jeffqchen/PS2VGA/Pics/3dprinting.jpg

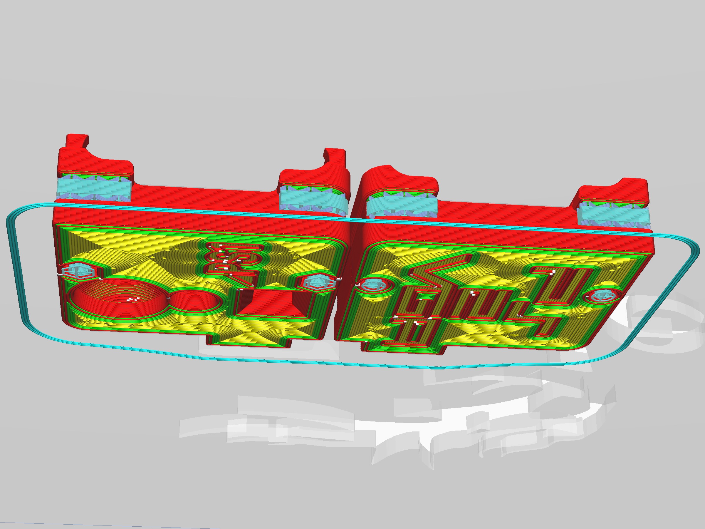
Pics/3dprinting.jpg
