jeffqchen/PS2VGA/Pics/ha_hole.jpg

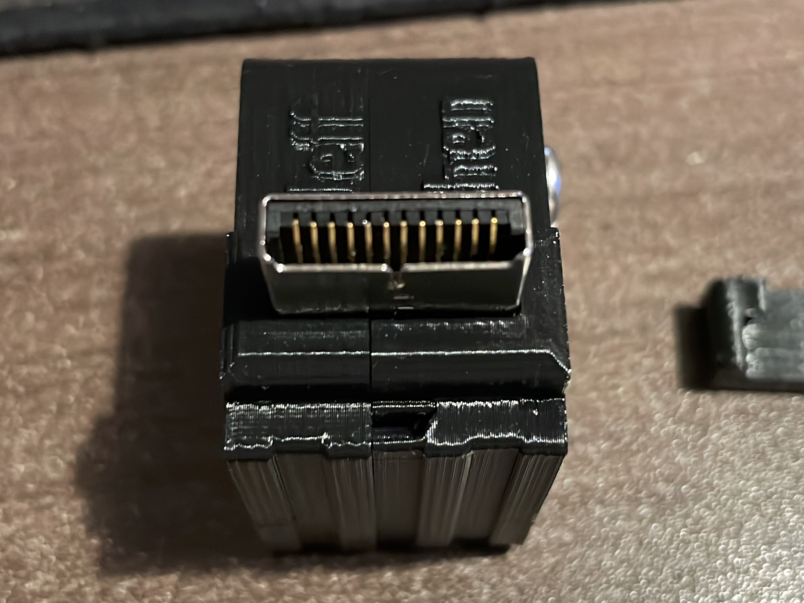
Pics/ha_hole.jpg
