jeffqchen/PS2VGA/Pics/ha_in.jpg

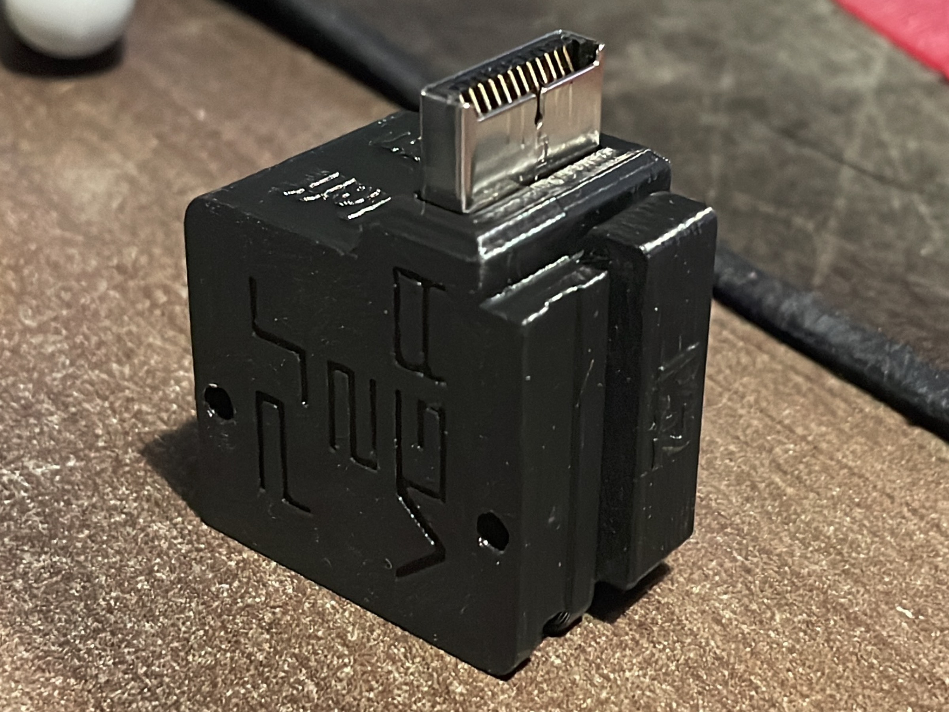
Pics/ha_in.jpg
