jeffqchen/PS2VGA/Pics/ha_ps1.jpg

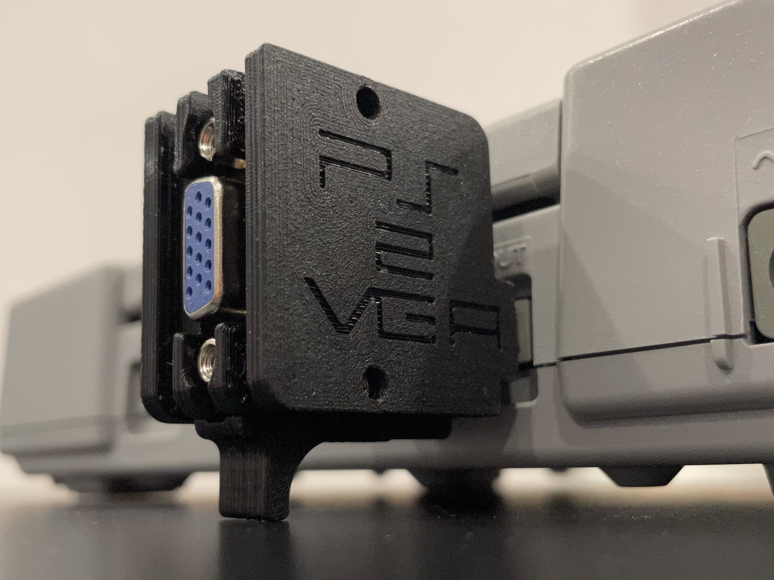
Pics/ha_ps1.jpg
