jeffqchen/PS2VGA/Pics/ha_ps2_l.jpg

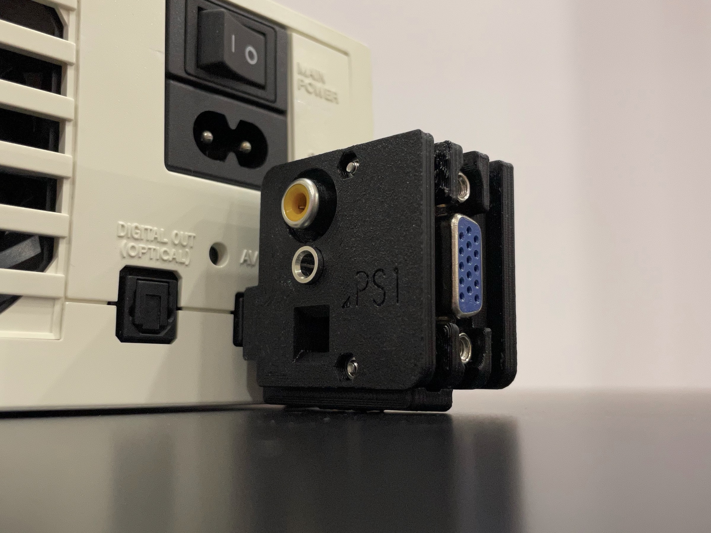
Pics/ha_ps2_l.jpg
