jeffqchen/PS2VGA/Pics/ha_ps2_r.jpg

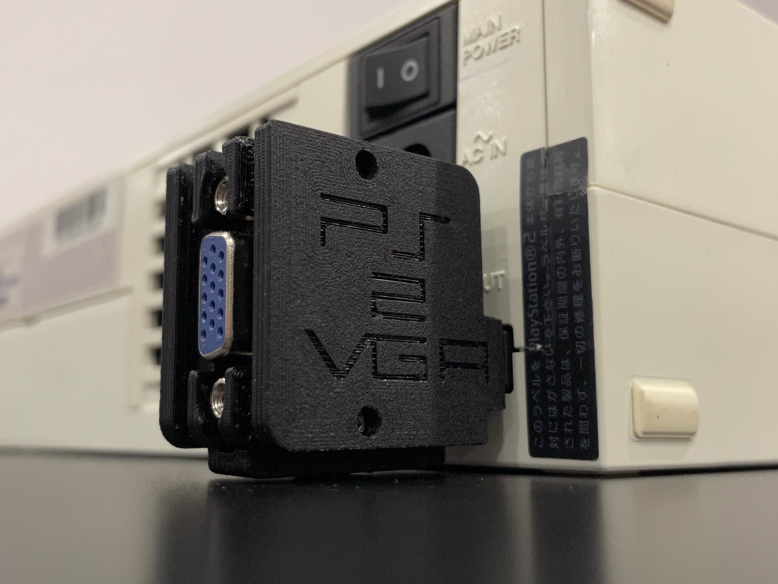
Pics/ha_ps2_r.jpg
