jeffqchen/PS2VGA/Pics/ha_ps2_slim1_l.jpg

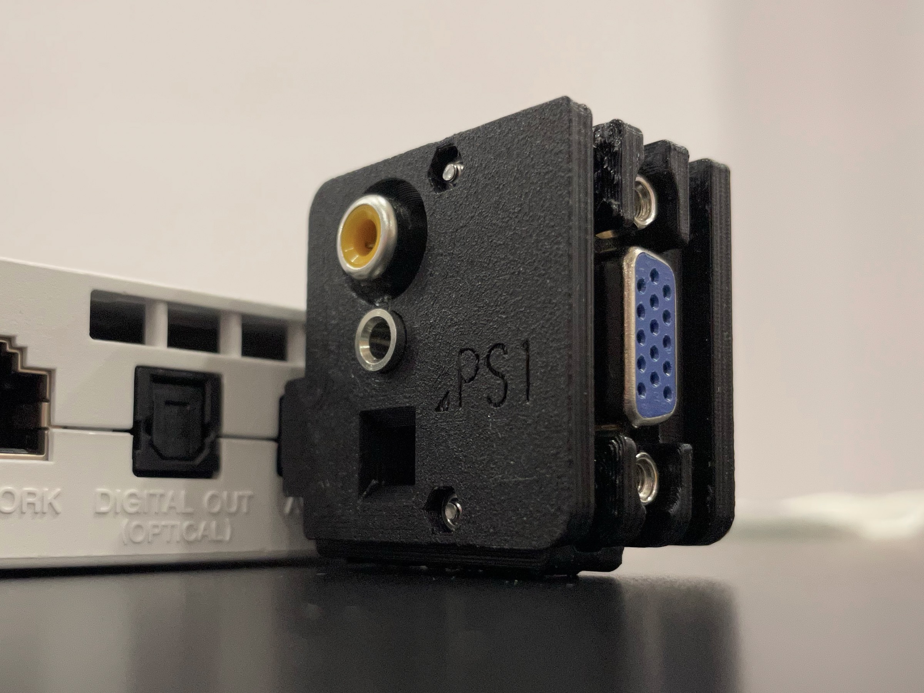
Pics/ha_ps2_slim1_l.jpg
