jeffqchen/PS2VGA/Pics/ha_ps2_slim1_r.jpg

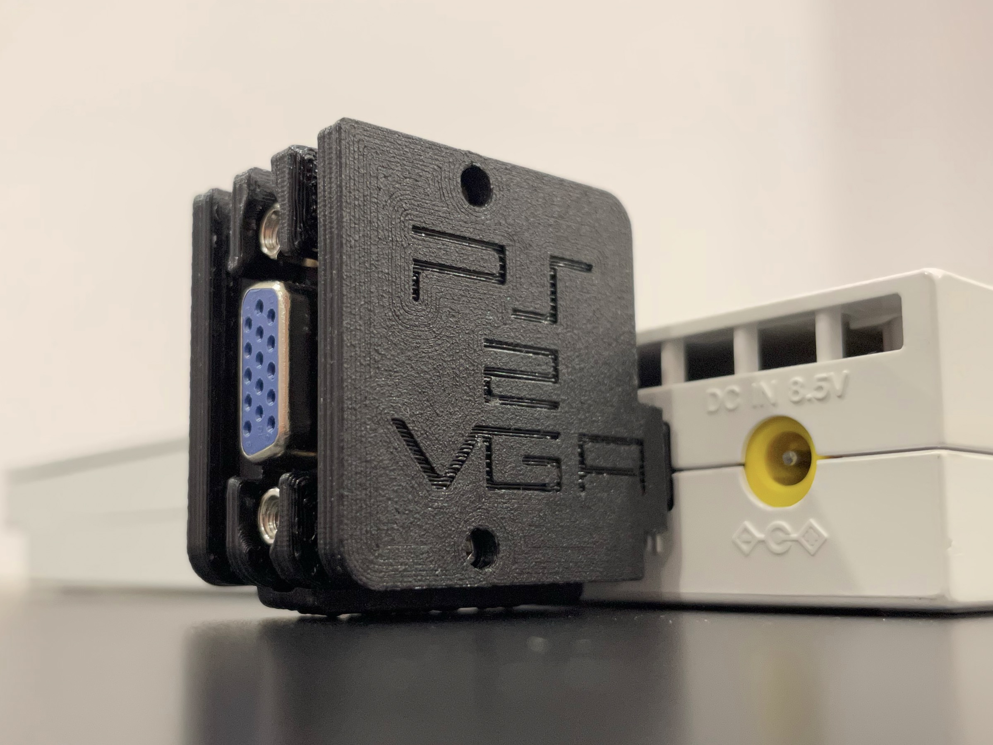
Pics/ha_ps2_slim1_r.jpg
