jeffqchen/PS2VGA/Pics/ha_psone.jpg

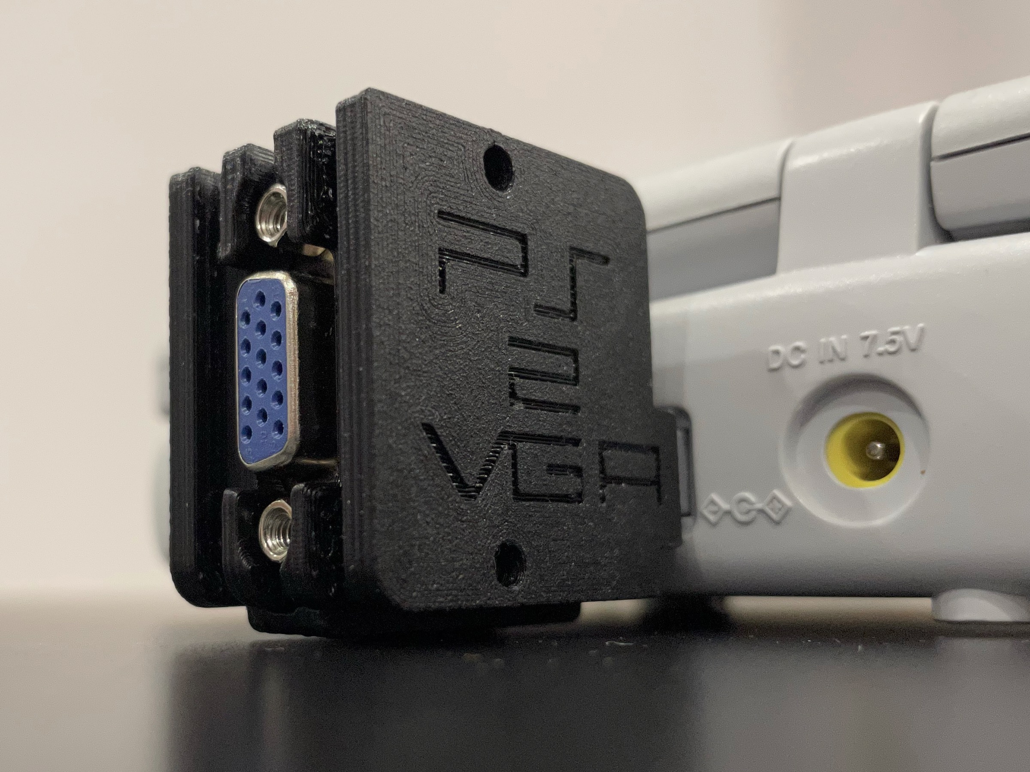
Pics/ha_psone.jpg
