jeffqchen/PS2VGA/Pics/height_adapters.jpg

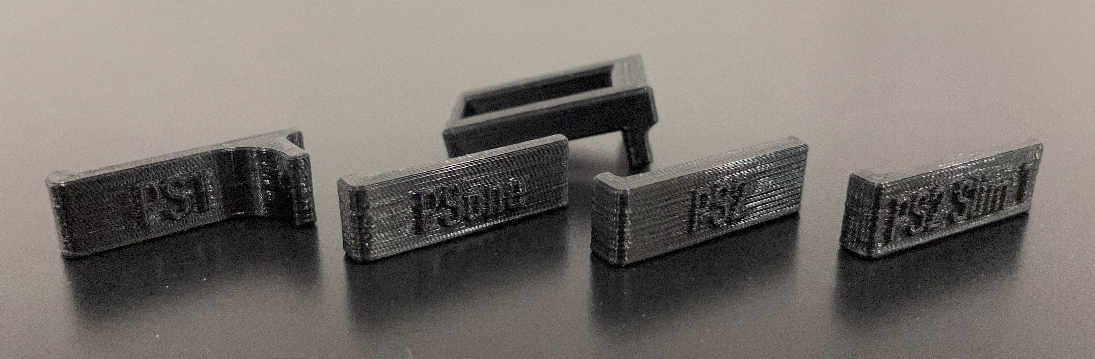
Pics/height_adapters.jpg
