jeffqchen/PS2VGA/Pics/lightgun.jpg

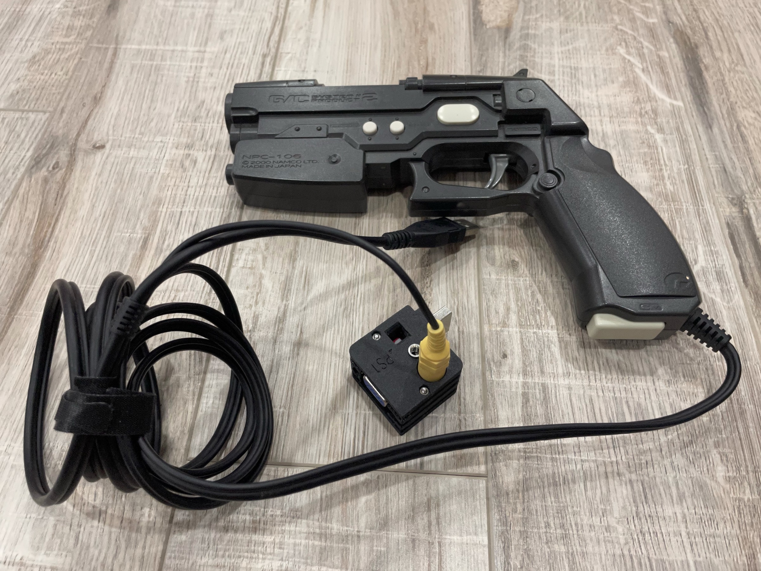
Pics/lightgun.jpg
