jeffqchen/PS2VGA/Pics/pcb.jpg

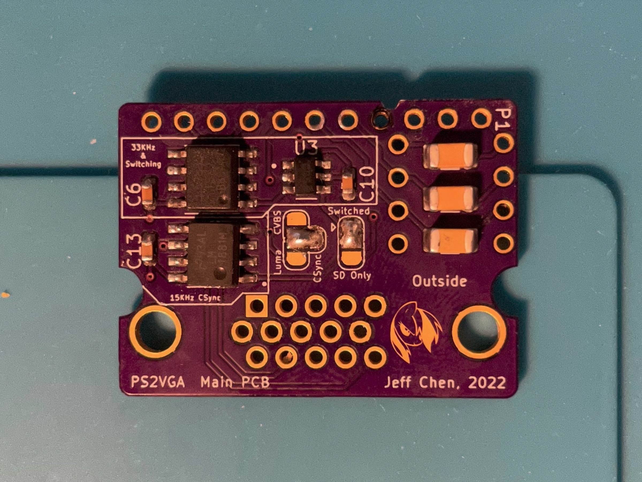
Pics/pcb.jpg
