jeffqchen/PS2VGA/Pics/ps2_slim2_l.jpg

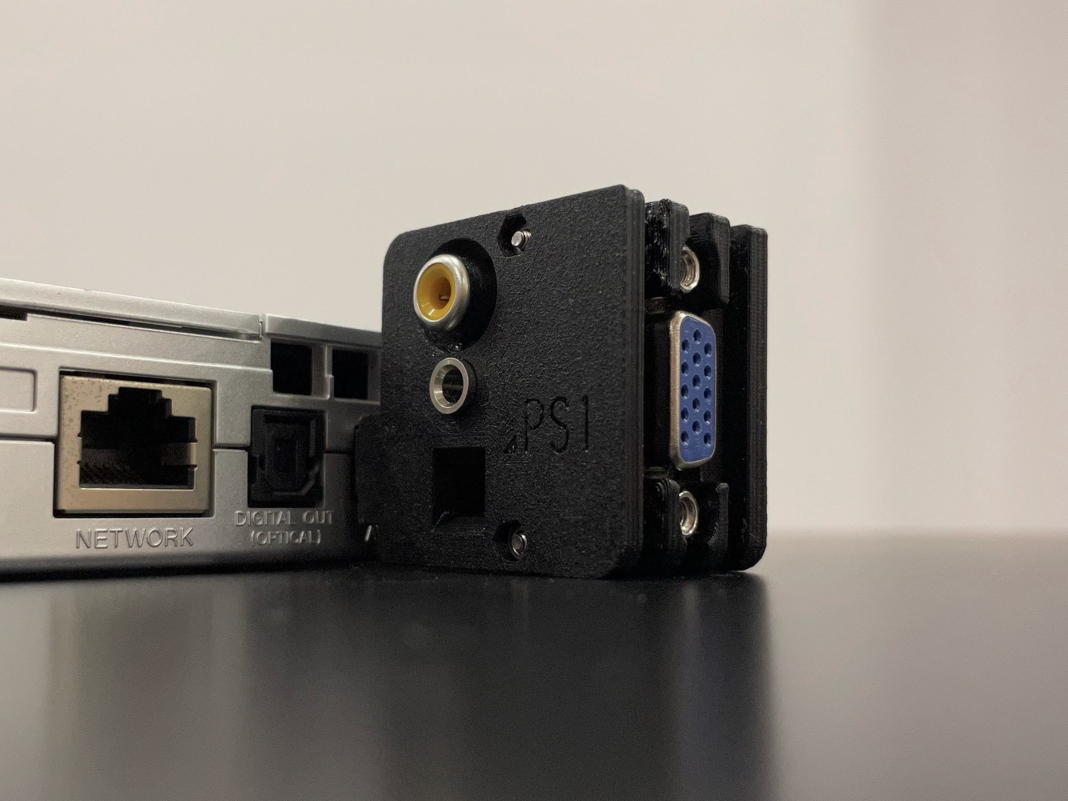
Pics/ps2_slim2_l.jpg
