jeffqchen/PS2VGA/Pics/ps2_slim2_r.jpg

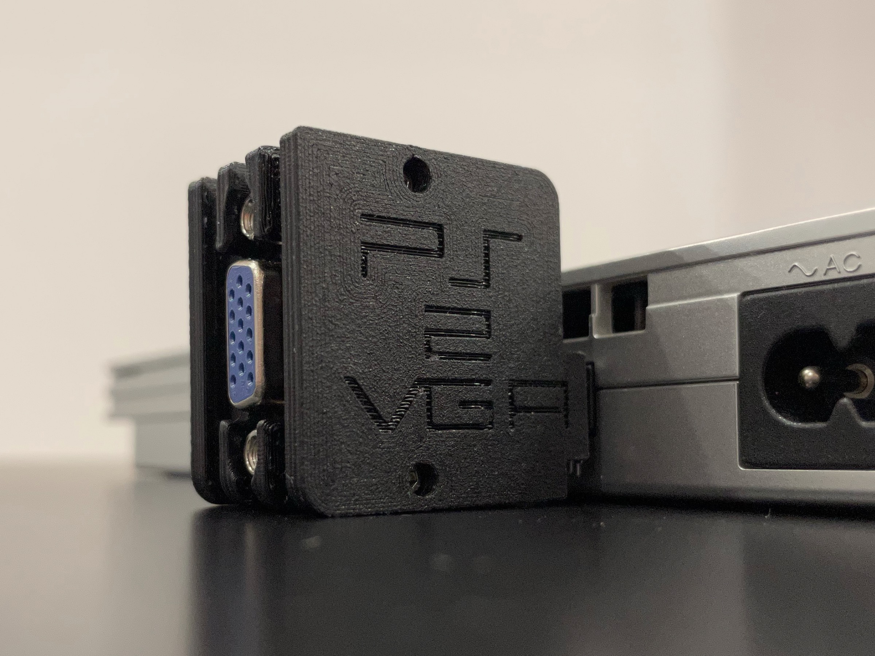
Pics/ps2_slim2_r.jpg
