jeffqchen/PS2VGA/Pics/ps3.jpg

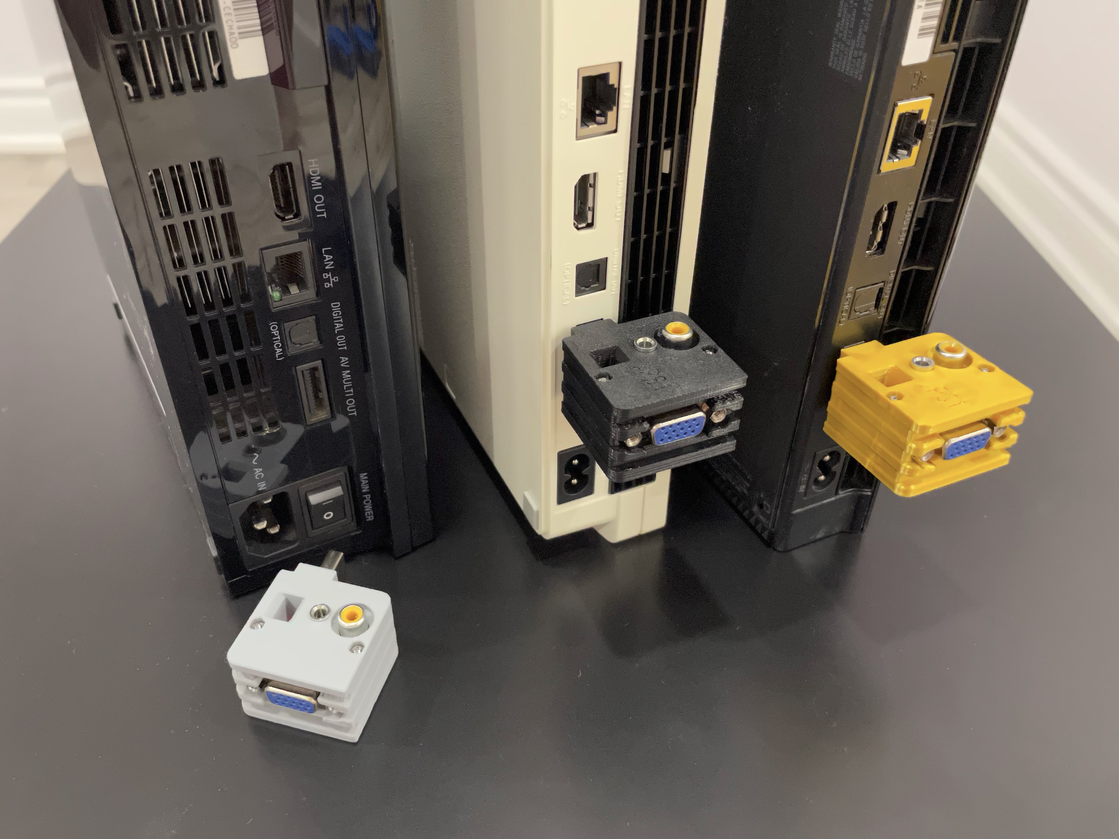
Pics/ps3.jpg
