jeffqchen/PS2VGA/Pics/vertical_adapter.jpg

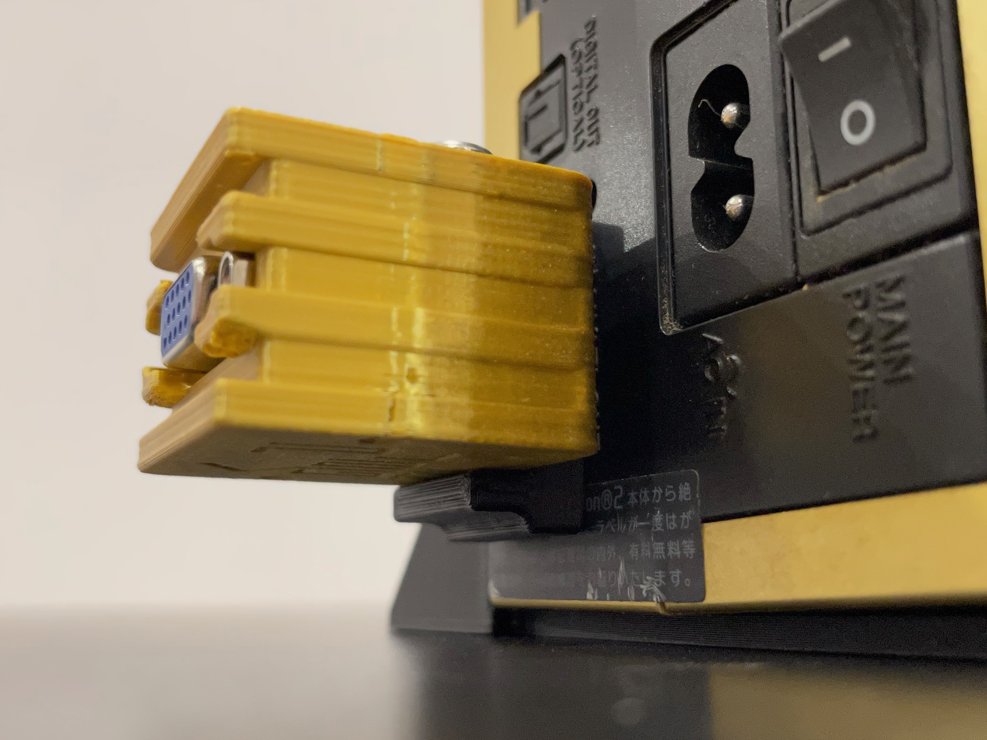
Pics/vertical_adapter.jpg
