jeffqchen/PS2VGA/Pics/assembly_final_01.jpg

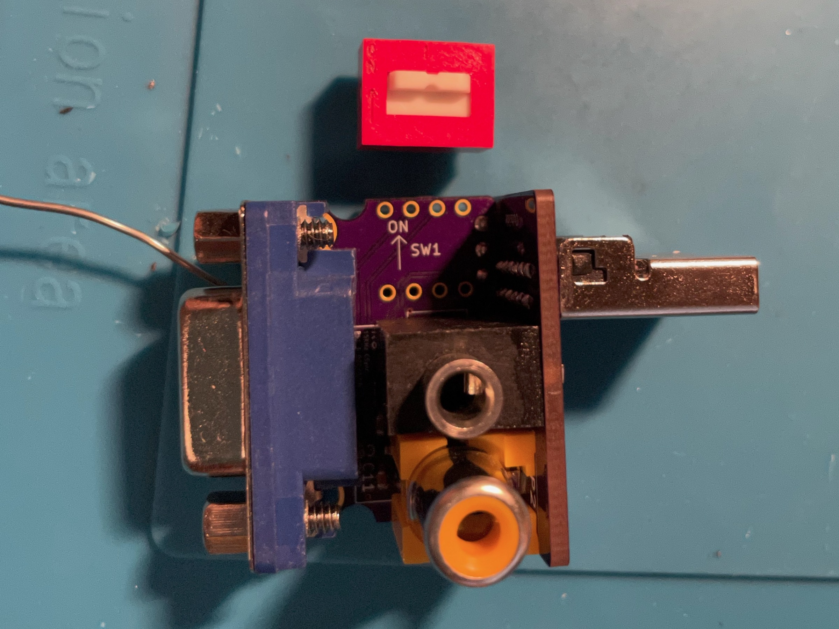
Pics/assembly_final_01.jpg
