jeffqchen/PS2VGA/Pics/assembly_final_02.jpg

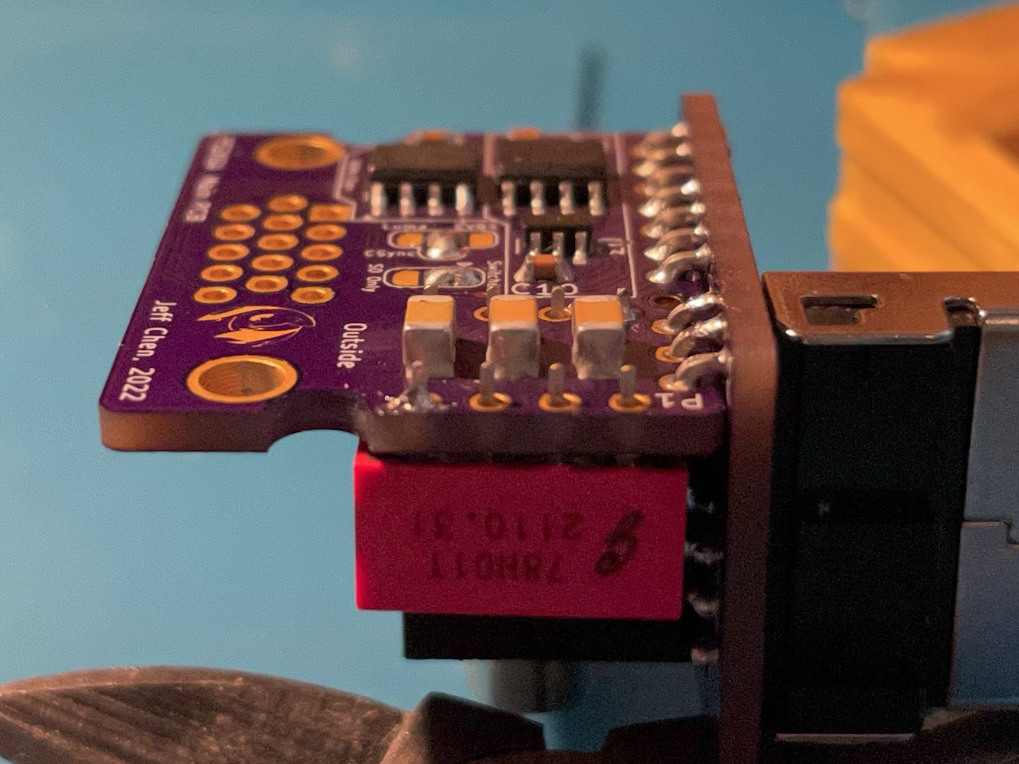
Pics/assembly_final_02.jpg
