jeffqchen/PS2VGA/Pics/assembly_final_03.jpg

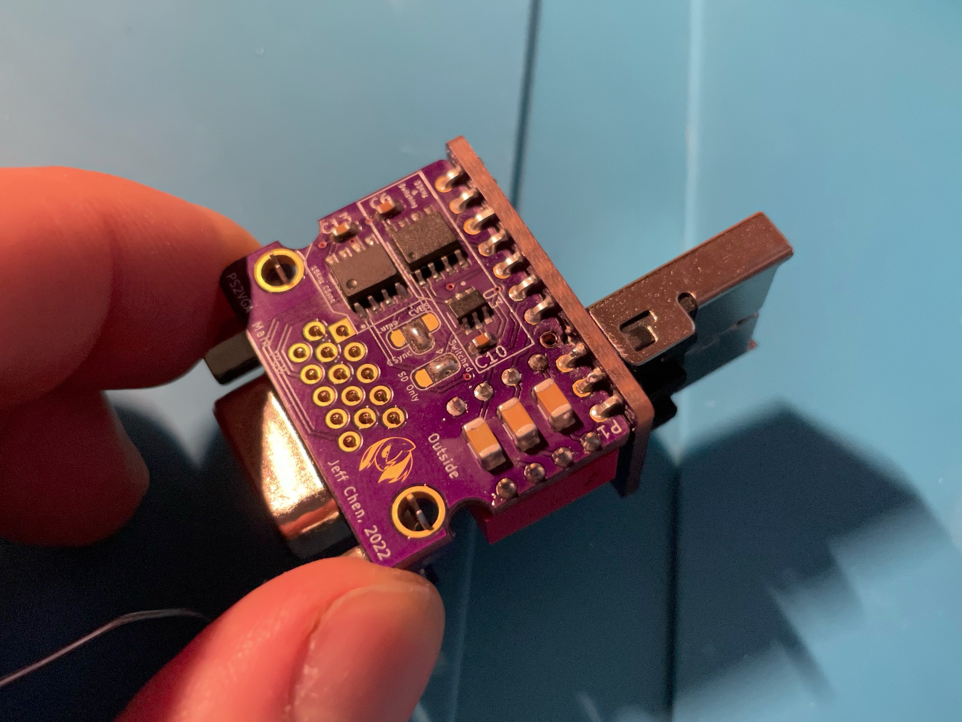
Pics/assembly_final_03.jpg
