jeffqchen/PS2VGA/Pics/assembly_final_05.jpg

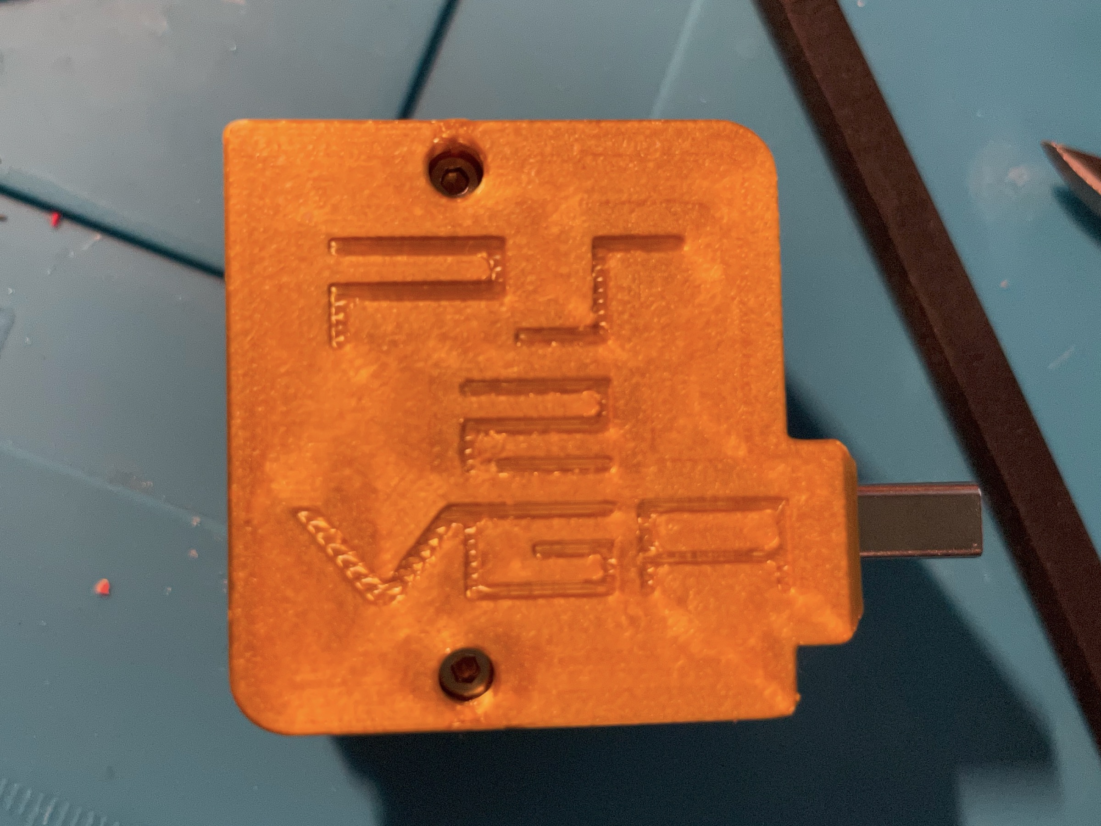
Pics/assembly_final_05.jpg
