jeffqchen/PS2VGA/Pics/assembly_final_06.jpg

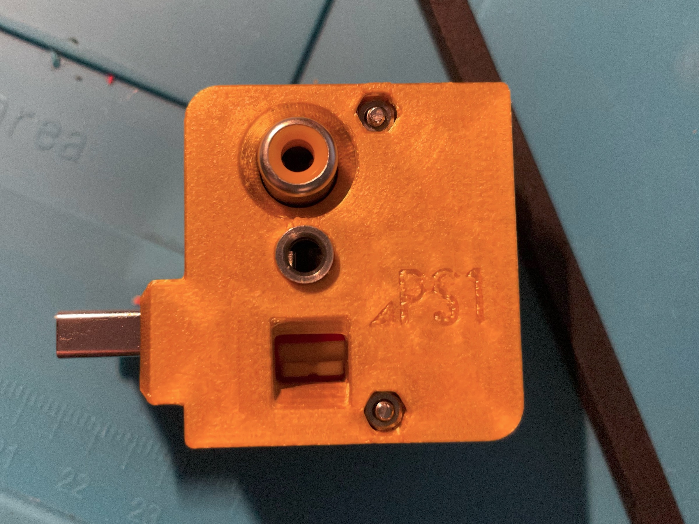
Pics/assembly_final_06.jpg
