jeffqchen/PS2VGA/Pics/assembly_pins_01.jpg

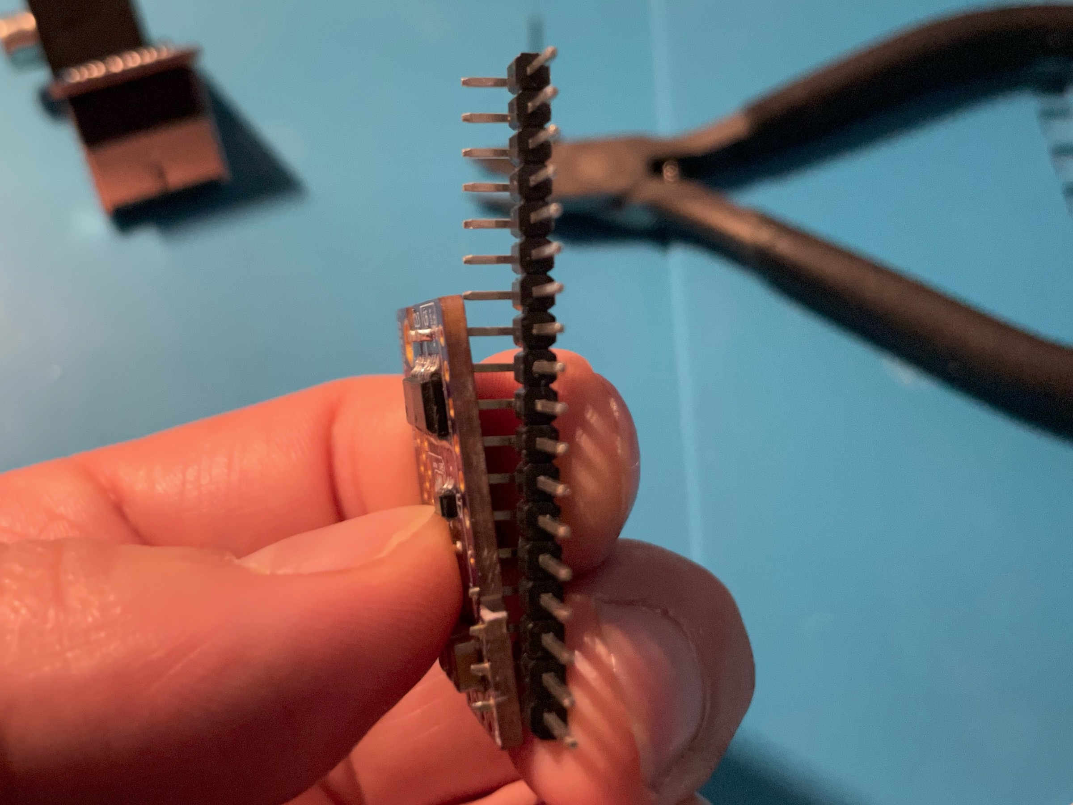
Pics/assembly_pins_01.jpg
