jeffqchen/PS2VGA/Pics/assembly_pins_02.jpg

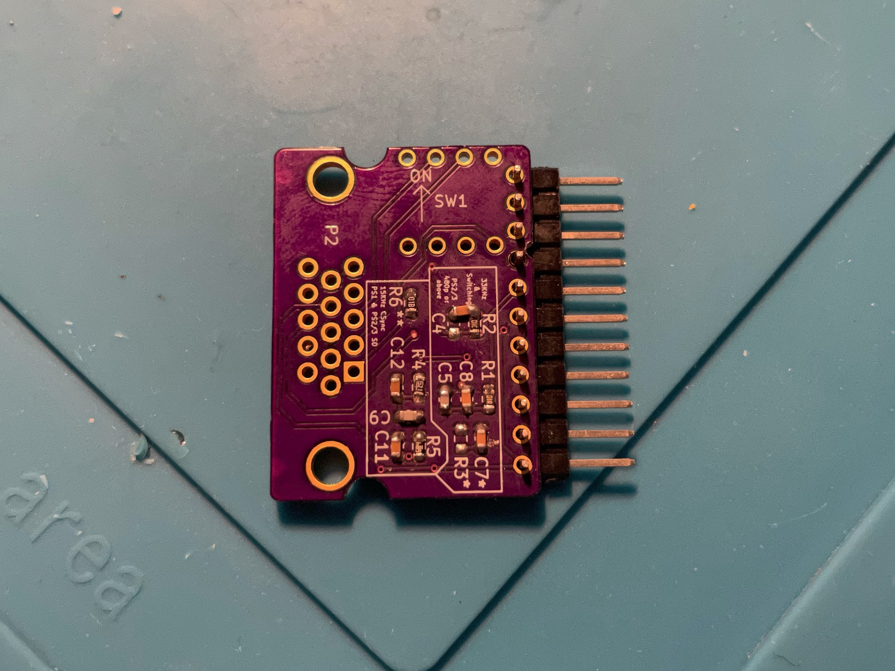
Pics/assembly_pins_02.jpg
