jeffqchen/PS2VGA/Pics/assembly_pins_03.jpg

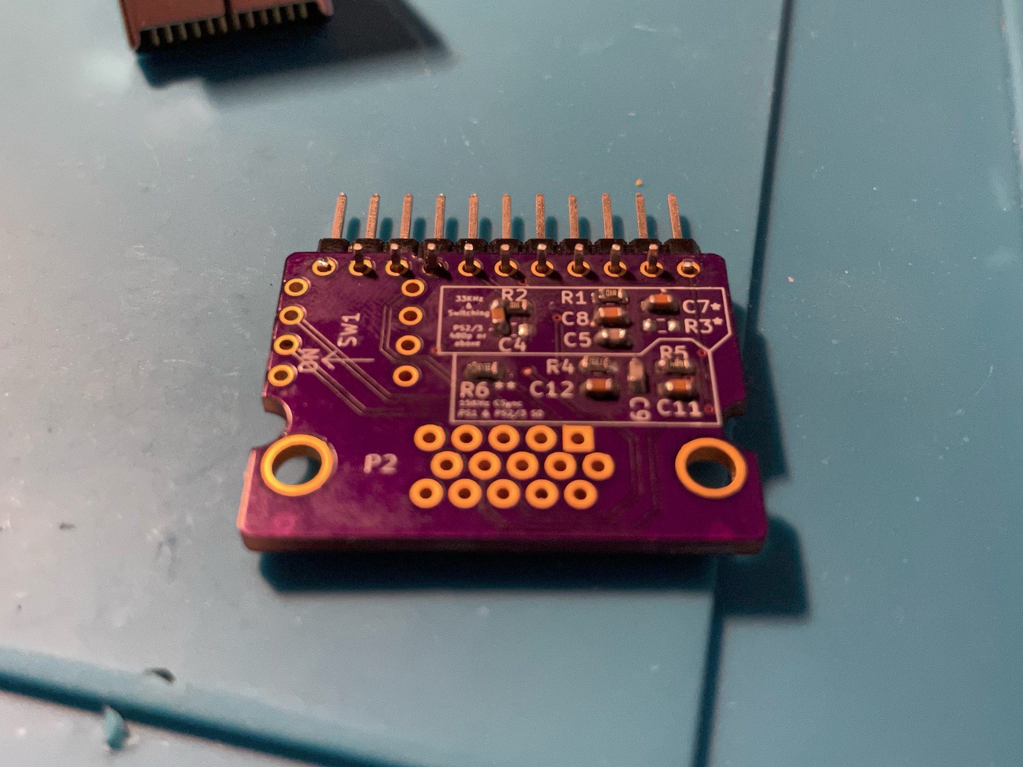
Pics/assembly_pins_03.jpg
