jeffqchen/PS2VGA/Pics/assembly_pins_05.jpg

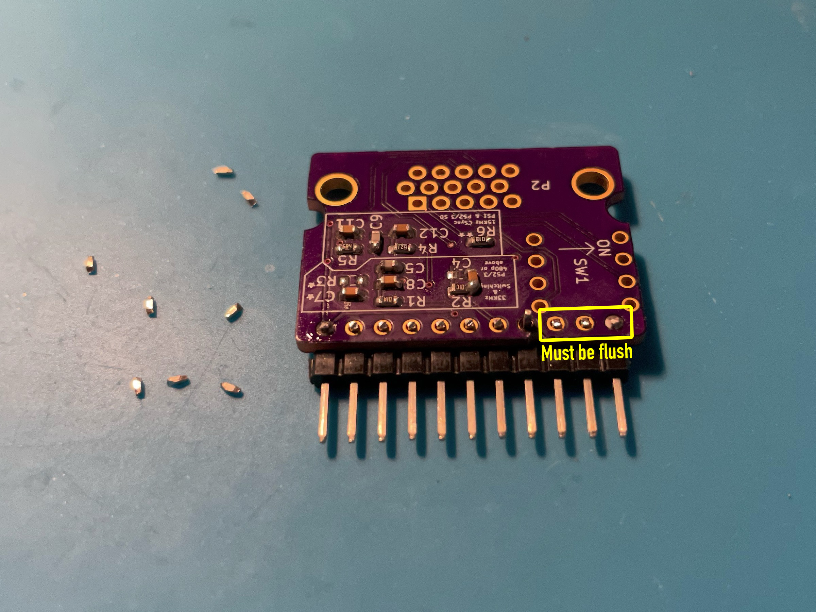
Pics/assembly_pins_05.jpg
