jeffqchen/PS2VGA/Pics/assembly_pins_06.jpg

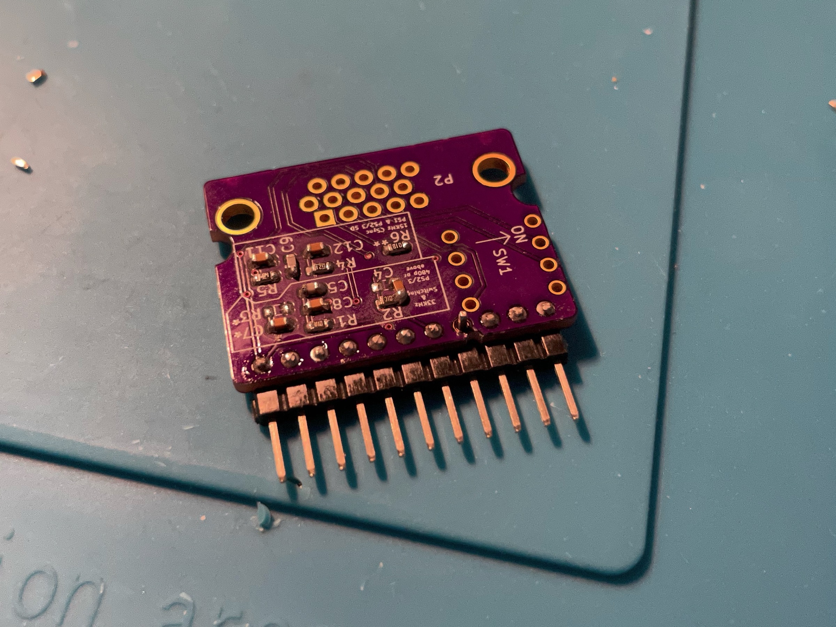
Pics/assembly_pins_06.jpg
