jeffqchen/PS2VGA/Pics/assembly_pins_07.jpg

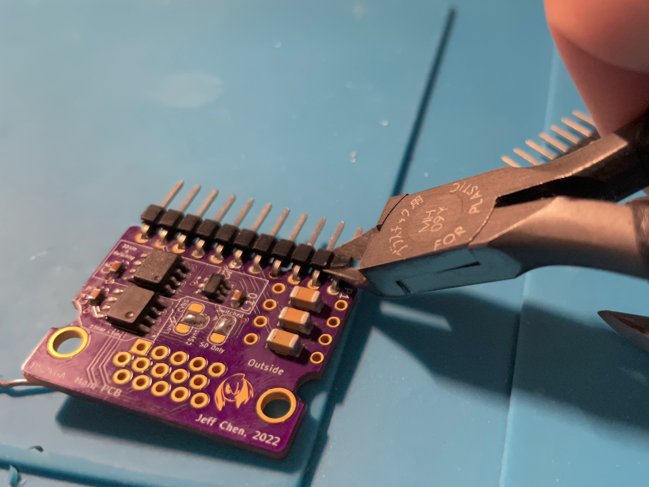
Pics/assembly_pins_07.jpg
