jeffqchen/PS2VGA/Pics/assembly_pins_10.jpg

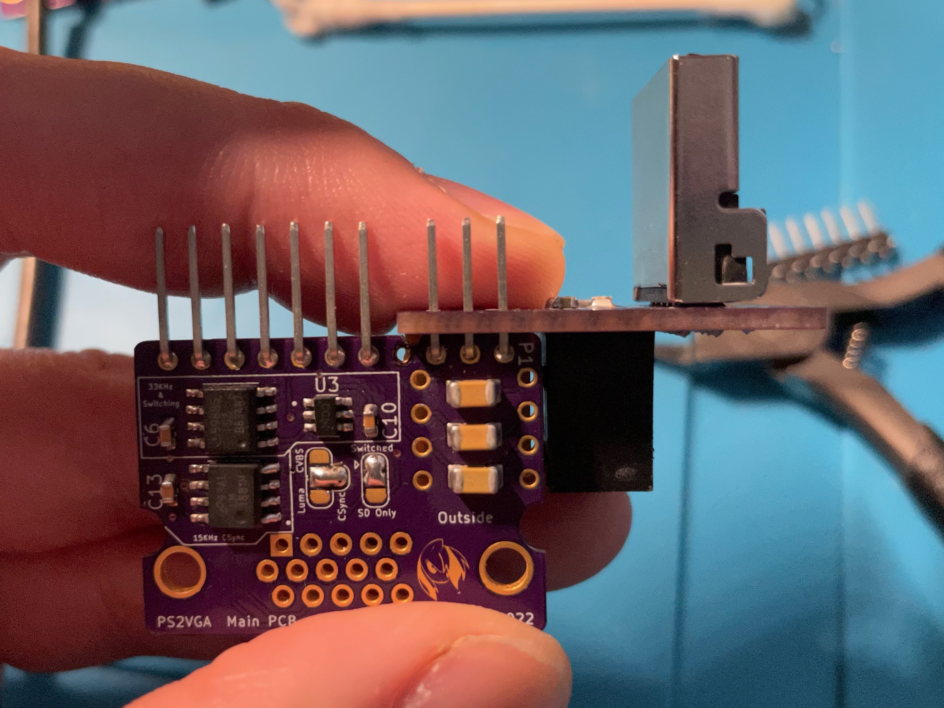
Pics/assembly_pins_10.jpg
