jeffqchen/PS2VGA/Pics/assembly_pins_11.jpg

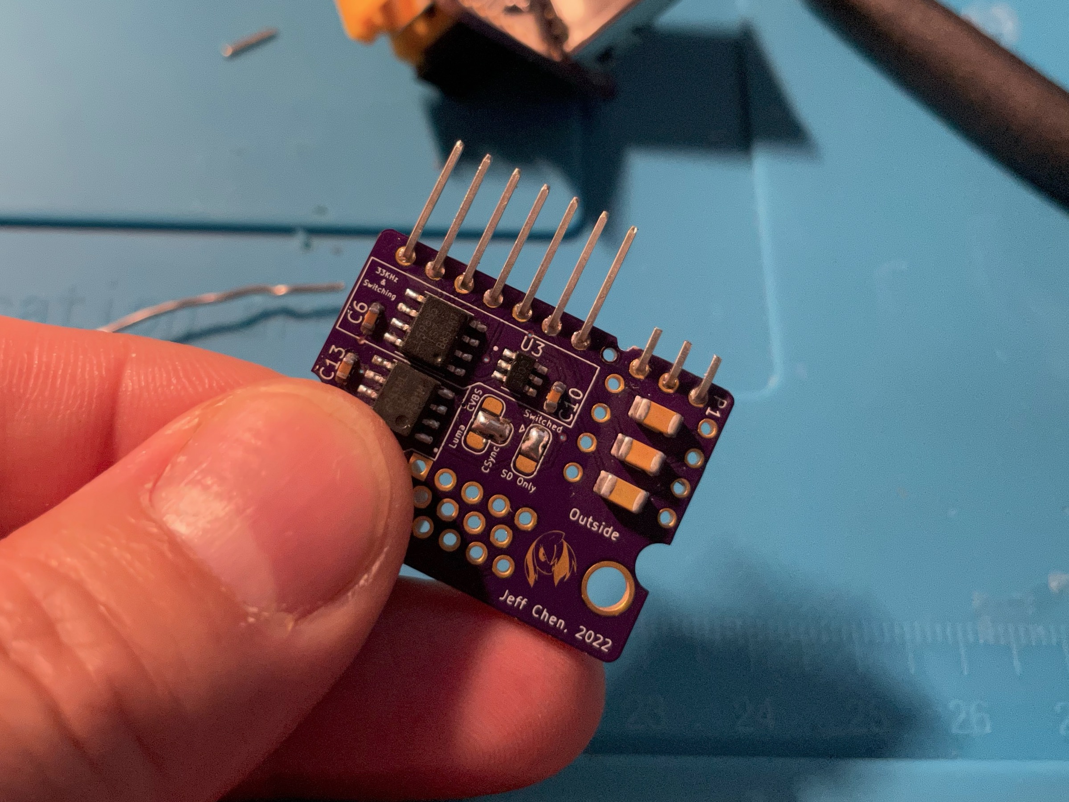
Pics/assembly_pins_11.jpg
