jeffqchen/PS2VGA/Pics/assembly_pins_12.jpg

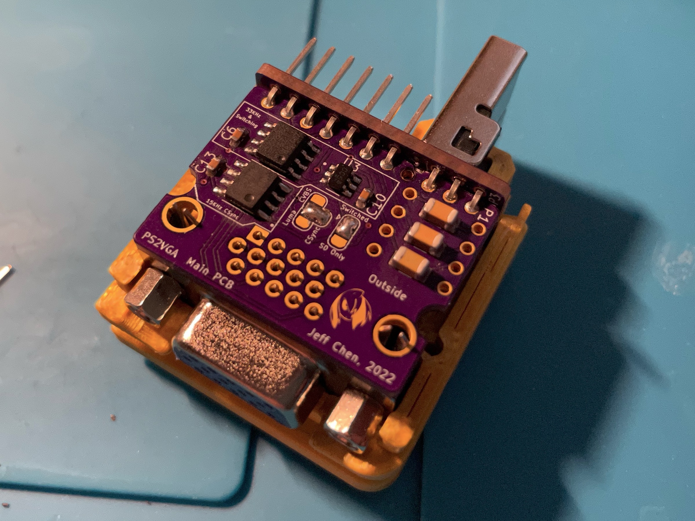
Pics/assembly_pins_12.jpg
