jeffqchen/PS2VGA/Pics/assembly_pins_13.jpg

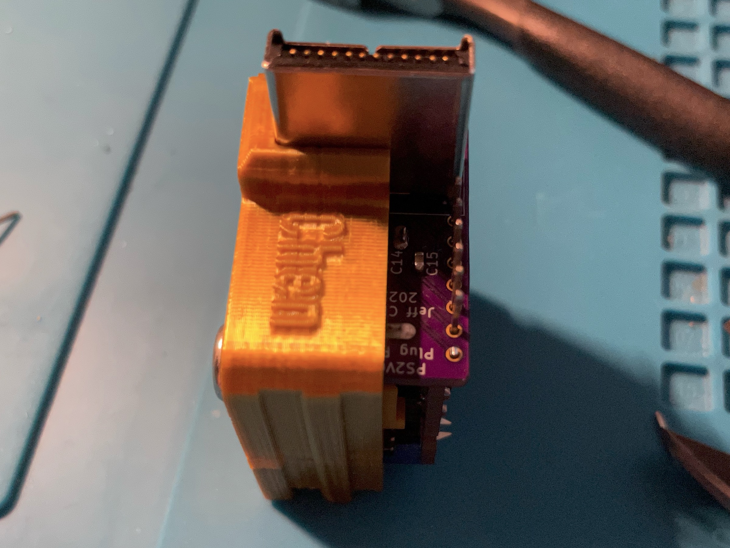
Pics/assembly_pins_13.jpg
