jeffqchen/PS2VGA/Pics/assembly_pins_14.jpg

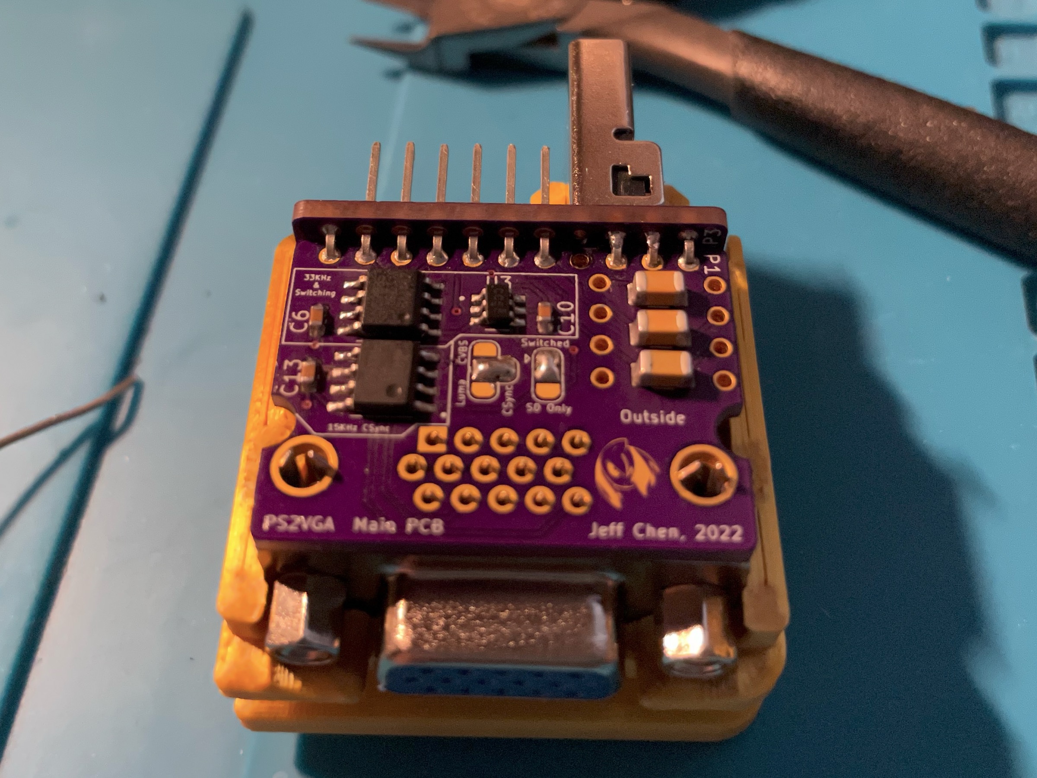
Pics/assembly_pins_14.jpg
