jeffqchen/PS2VGA/Pics/assembly_pins_15.jpg

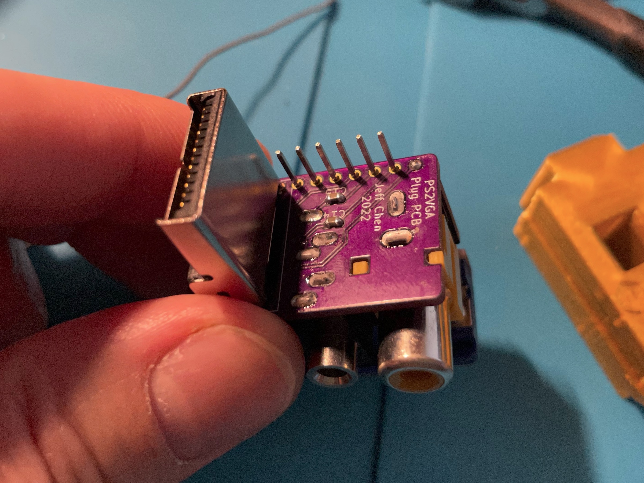
Pics/assembly_pins_15.jpg
