jeffqchen/PS2VGA/Pics/assembly_pins_16.jpg

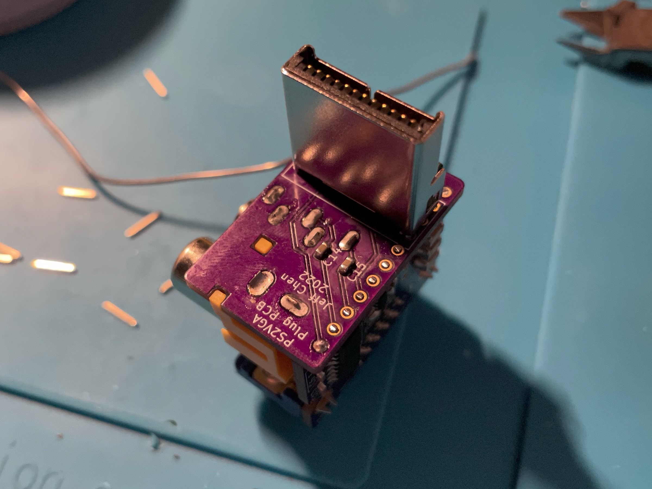
Pics/assembly_pins_16.jpg
