jeffqchen/PS2VGA/Pics/assembly_pins_17.jpg

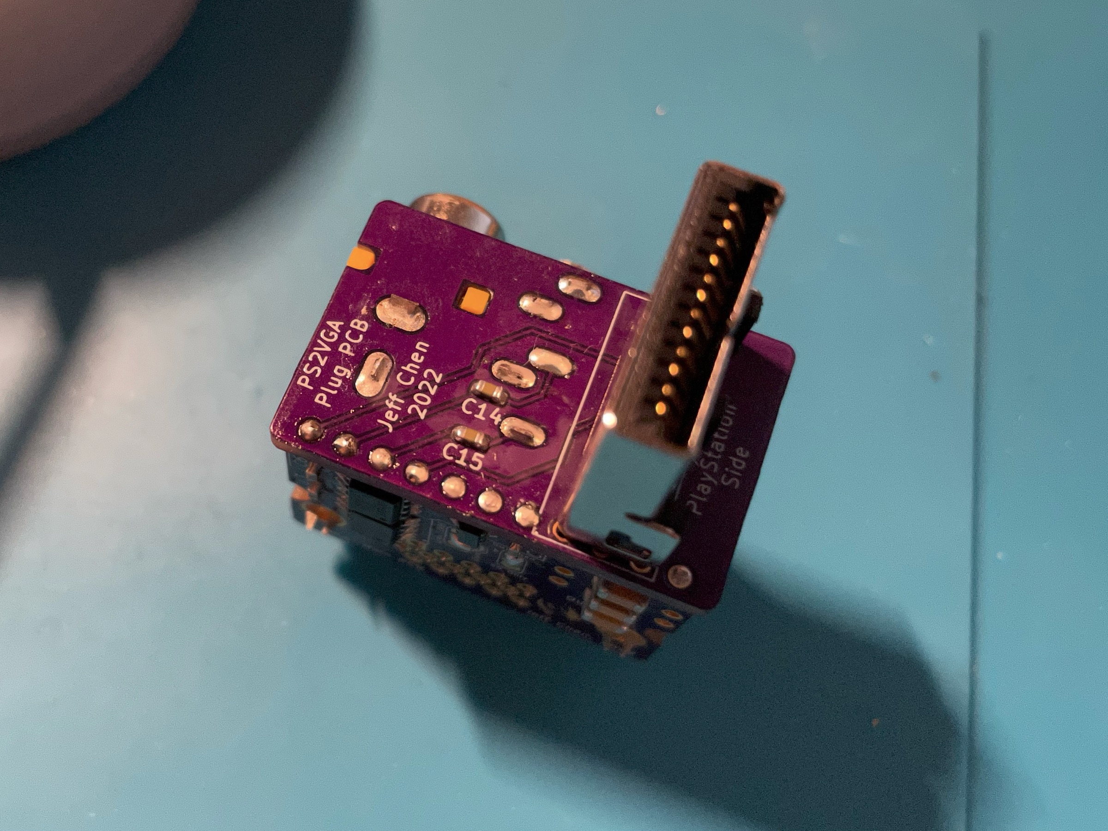
Pics/assembly_pins_17.jpg
