jeffqchen/PS2VGA/Pics/assembly_smd_01.jpg

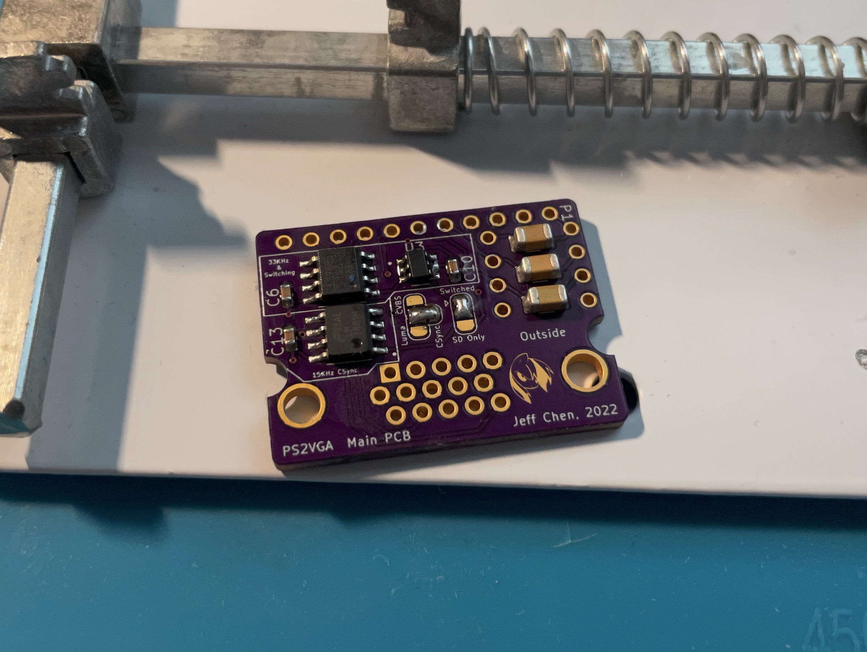
Pics/assembly_smd_01.jpg
