jeffqchen/PS2VGA/Pics/assembly_smd_03.jpg

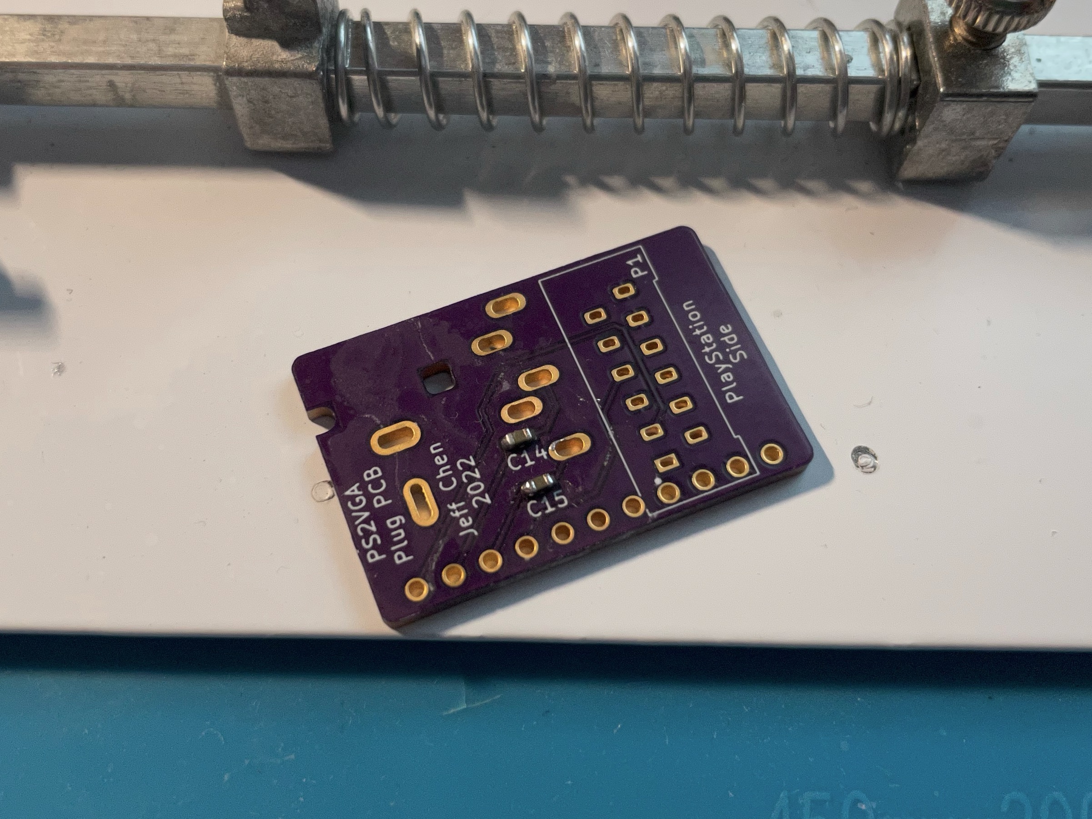
Pics/assembly_smd_03.jpg
