jeffqchen/PS2VGA/Pics/assembly_thd_01.jpg

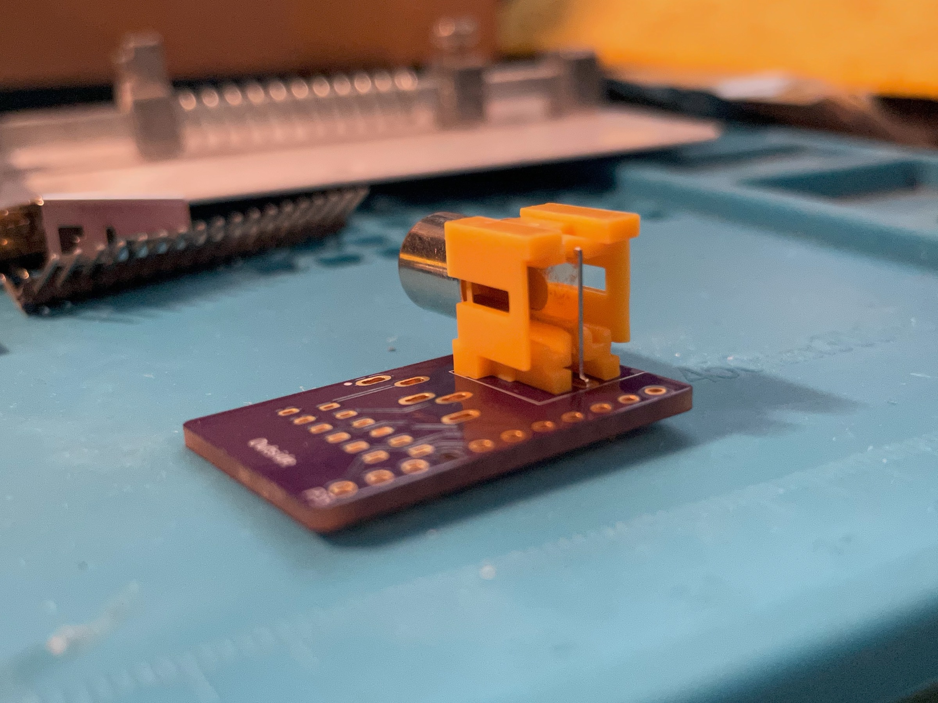
Pics/assembly_thd_01.jpg
