jeffqchen/PS2VGA/Pics/assembly_thd_02.jpg

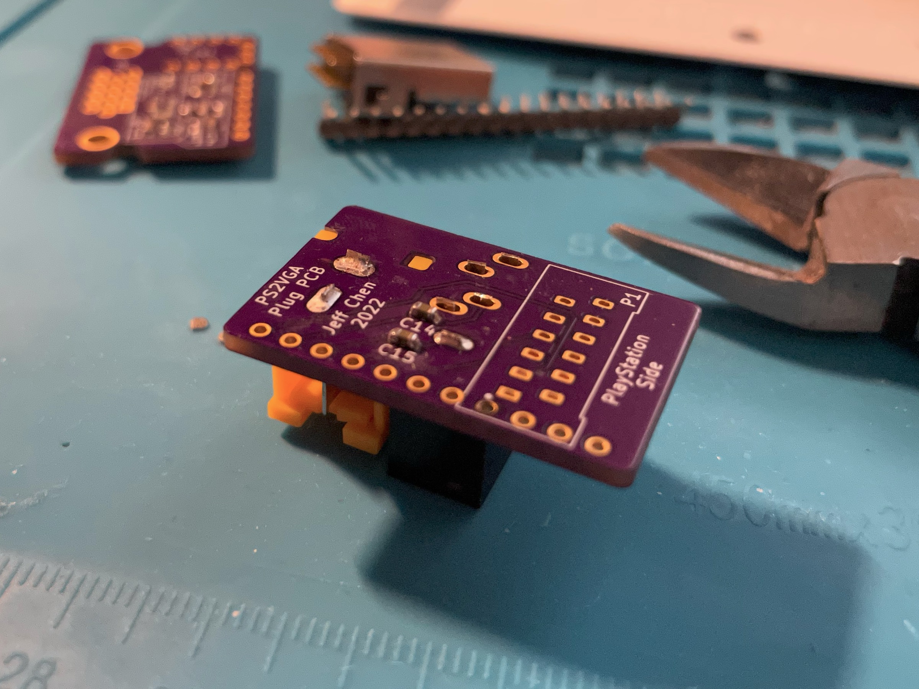
Pics/assembly_thd_02.jpg
