jeffqchen/PS2VGA/Pics/assembly_thd_04.jpg

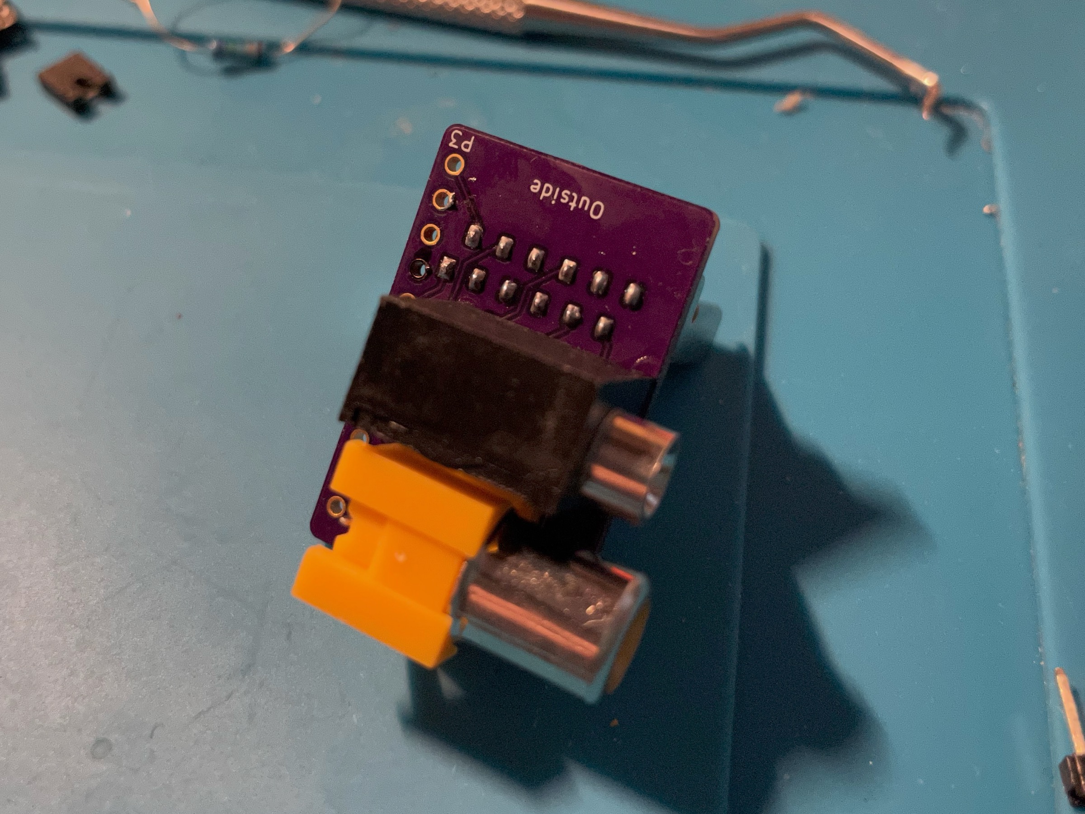
Pics/assembly_thd_04.jpg
