jeffqchen/PS2VGA/Pics/assembly_thd_05.jpg

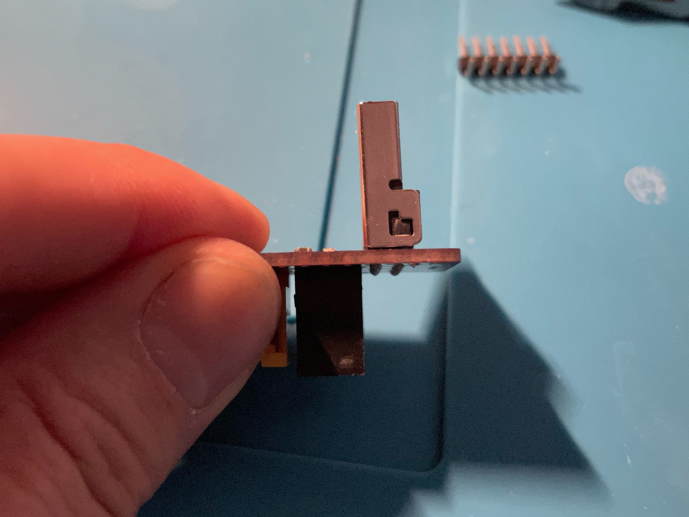
Pics/assembly_thd_05.jpg
